Threadnaught/amper/1606firmware/chars.h

#include <avr/pgmspace.h>

//  Bit layout : 0bBCEDFAPG

const unsigned char chars[] PROGMEM = {
	'\x01', // -
	'\x01', // -
	'\x01', // -
	'\x01', // -
	'\x01', // -
	'\x01', // -
	'\x01', // -
	'\x01', // -
	'\x01', // -
	'\x01', // -
	'\x01', // -
	'\x01', // -
	'\x01', // -
	'\x01', // -
	'\x01', // -
	'\x01', // -
	'\x01', // -
	'\x01', // -
	'\x01', // -
	'\x01', // -
	'\x01', // -
	'\x01', // -
	'\x01', // -
	'\x01', // -
	'\x01', // -
	'\x01', // -
	'\x01', // -
	'\x01', // -
	'\x01', // -
	'\x01', // -
	'\x01', // -
	'\x01', // -
	'\x01', // -
	'\x01', // -
	'\x01', // -
	'\x01', // -
	'\x01', // -
	'\x01', // -
	'\x01', // -
	'\x01', // -
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
	'\xfc', // 0
	'\xc0', // 1
	'\xb5', // 2
	'\xd5', // 3
	'\xc9', // 4
	'\x5d', // 5
	'\x7d', // 6
	'\xc4', // 7
	'\xfd', // 8
	'\xdd', // 9
	'\x01', // -
	'\x01', // -
	'\x01', // -
	'\x01', // -
	'\x01', // -
	'\x01', // -
	'\x01', // -
	'\x01', // -
	'\x01', // -
	'\x01', // -
	'\x01', // -
	'\x01', // -
	'\x01', // -
	'\x01', // -
	'\x01', // -
	'\x01', // -
	'\x01', // -
	'\x01', // -
	'\x01', // -
	'\x01', // -
	'\x01', // -
	'\x01', // -
	'\x01', // -
	'\x01', // -
	'\x01', // -
	'\x01', // -
	'\x01', // -
	'\x01', // -
	'\x01', // -
	'\x01', // -
	'\x01', // -
	'\x01', // -
	'\x01', // -
	'\x01', // -
	'\x01', // -
	'\x01', // -
	'\x01', // -
	'\x01', // -
	'\x01', // -
	'\x01', // -
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
};
