Threadnaught/amper/328pfirmware/chars.h

#include <avr/pgmspace.h>

const unsigned char chars[] PROGMEM = {
	'\x40', // -
	'\x40', // -
	'\x40', // -
	'\x40', // -
	'\x40', // -
	'\x40', // -
	'\x40', // -
	'\x40', // -
	'\x40', // -
	'\x40', // -
	'\x40', // -
	'\x40', // -
	'\x40', // -
	'\x40', // -
	'\x40', // -
	'\x40', // -
	'\x40', // -
	'\x40', // -
	'\x40', // -
	'\x40', // -
	'\x40', // -
	'\x40', // -
	'\x40', // -
	'\x40', // -
	'\x40', // -
	'\x40', // -
	'\x40', // -
	'\x40', // -
	'\x40', // -
	'\x40', // -
	'\x40', // -
	'\x40', // -
	'\x40', // -
	'\x40', // -
	'\x40', // -
	'\x40', // -
	'\x40', // -
	'\x40', // -
	'\x40', // -
	'\x40', // -
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
};
